teapotlaboratories/bwlr3d/docs/images/case_close.jpg

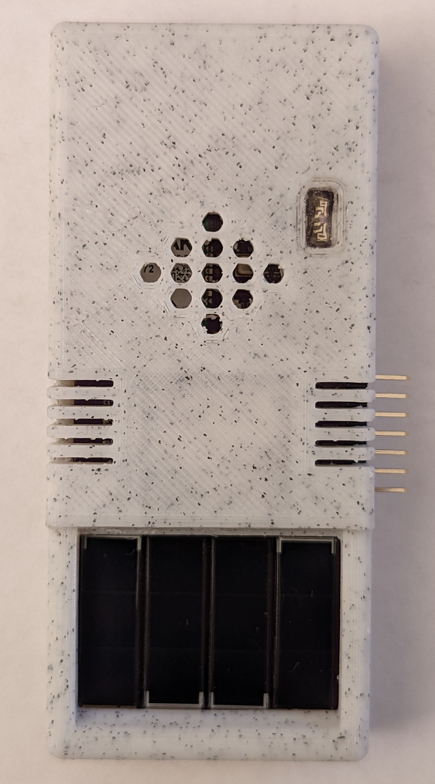
docs/images/case_close.jpg
