teapotlaboratories/bwlr3d/docs/images/device_close_up.jpg

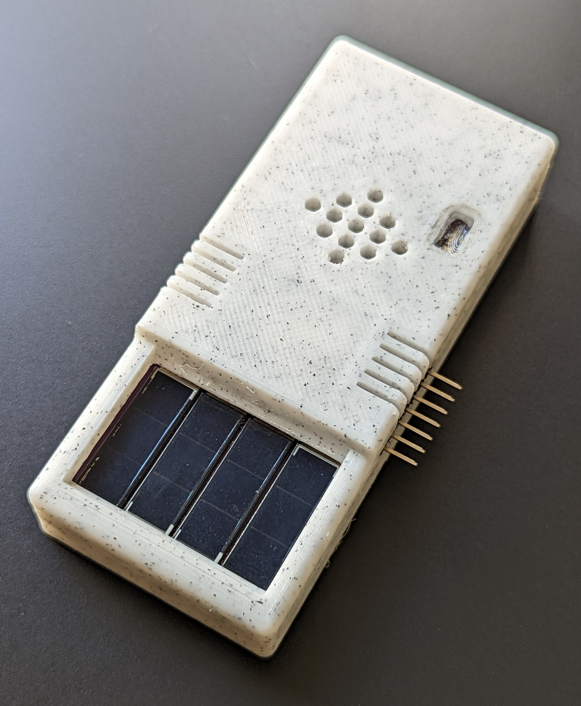
docs/images/device_close_up.jpg
