teapotlaboratories/bwlr3d/docs/images/standing_with_aa_for_comparison.jpg

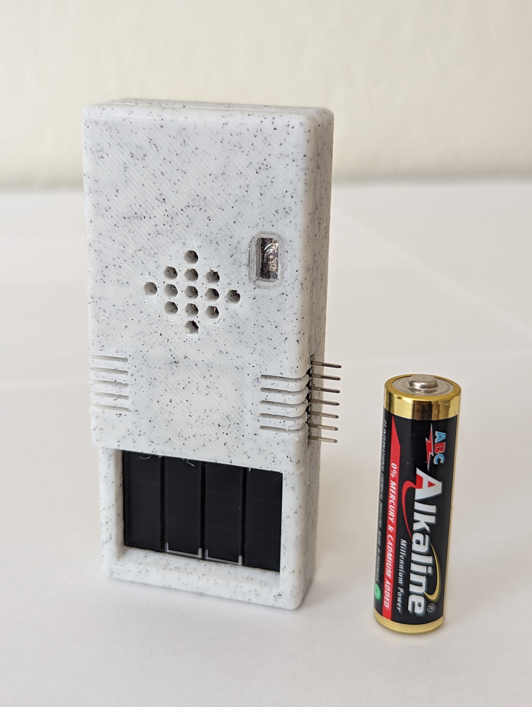
docs/images/standing_with_aa_for_comparison.jpg
