teapotlaboratories/bwlr3d/docs/images/with_aa_for_comparison.jpg

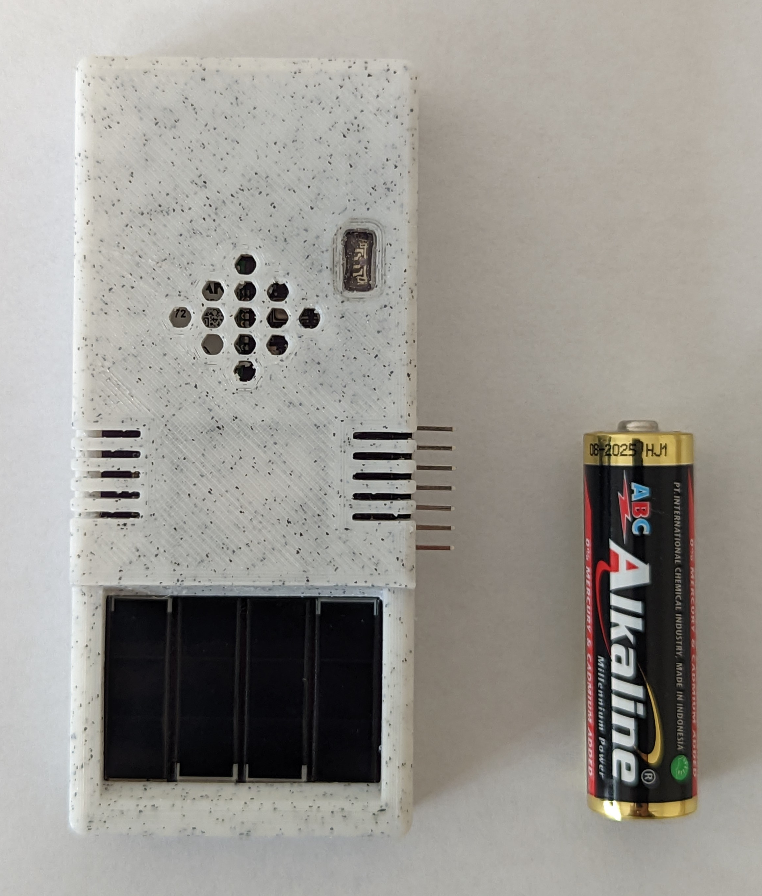
docs/images/with_aa_for_comparison.jpg
