teapotlaboratories/bwlr3d/hardware/pcb_bottom.png

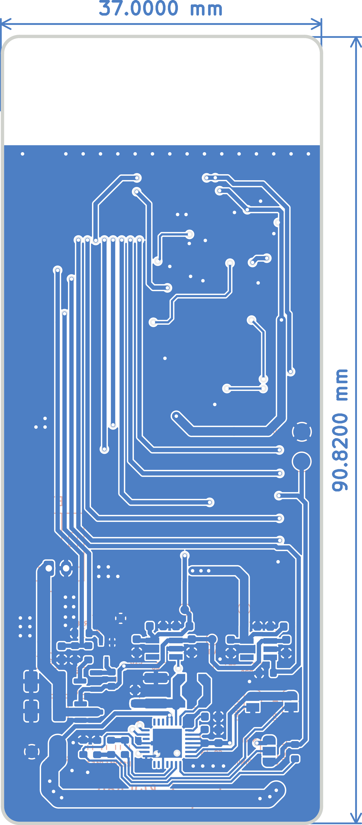
hardware/pcb_bottom.png
