teapotlaboratories/bwlr3d/hardware/pcb_top.png

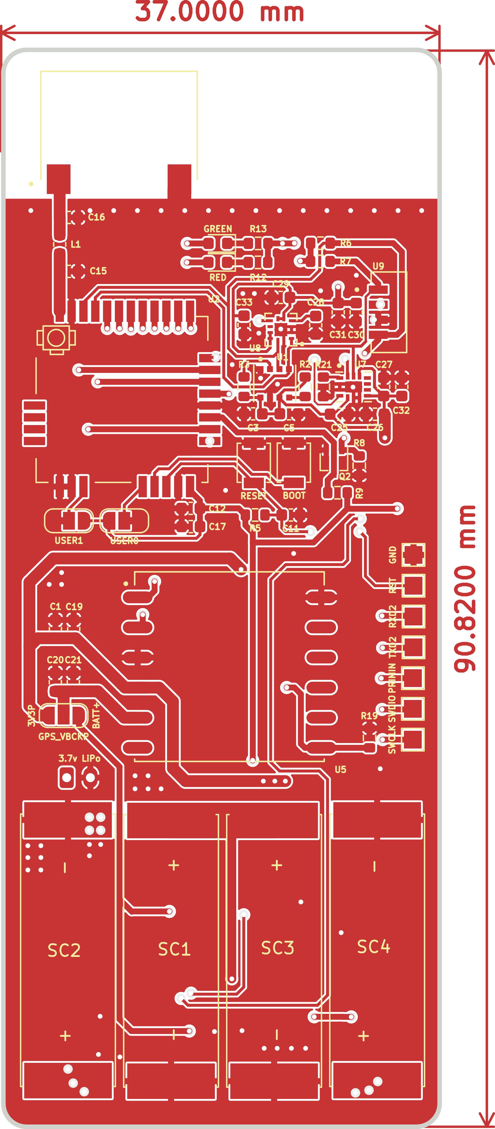
hardware/pcb_top.png
